atctwo/clock25/extras/images/web_main.png

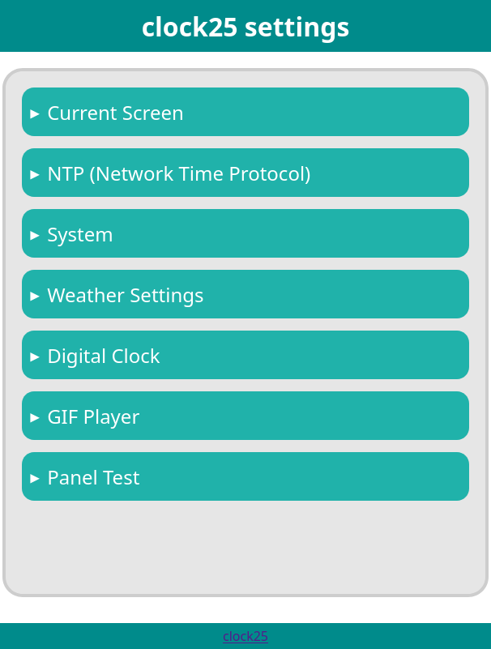
extras/images/web_main.png
