atctwo/clock25/pcb/clock25/clock25.kicad_sch

## KiCad design pcb/clock25/clock25.kicad_sch (2023-04-29)

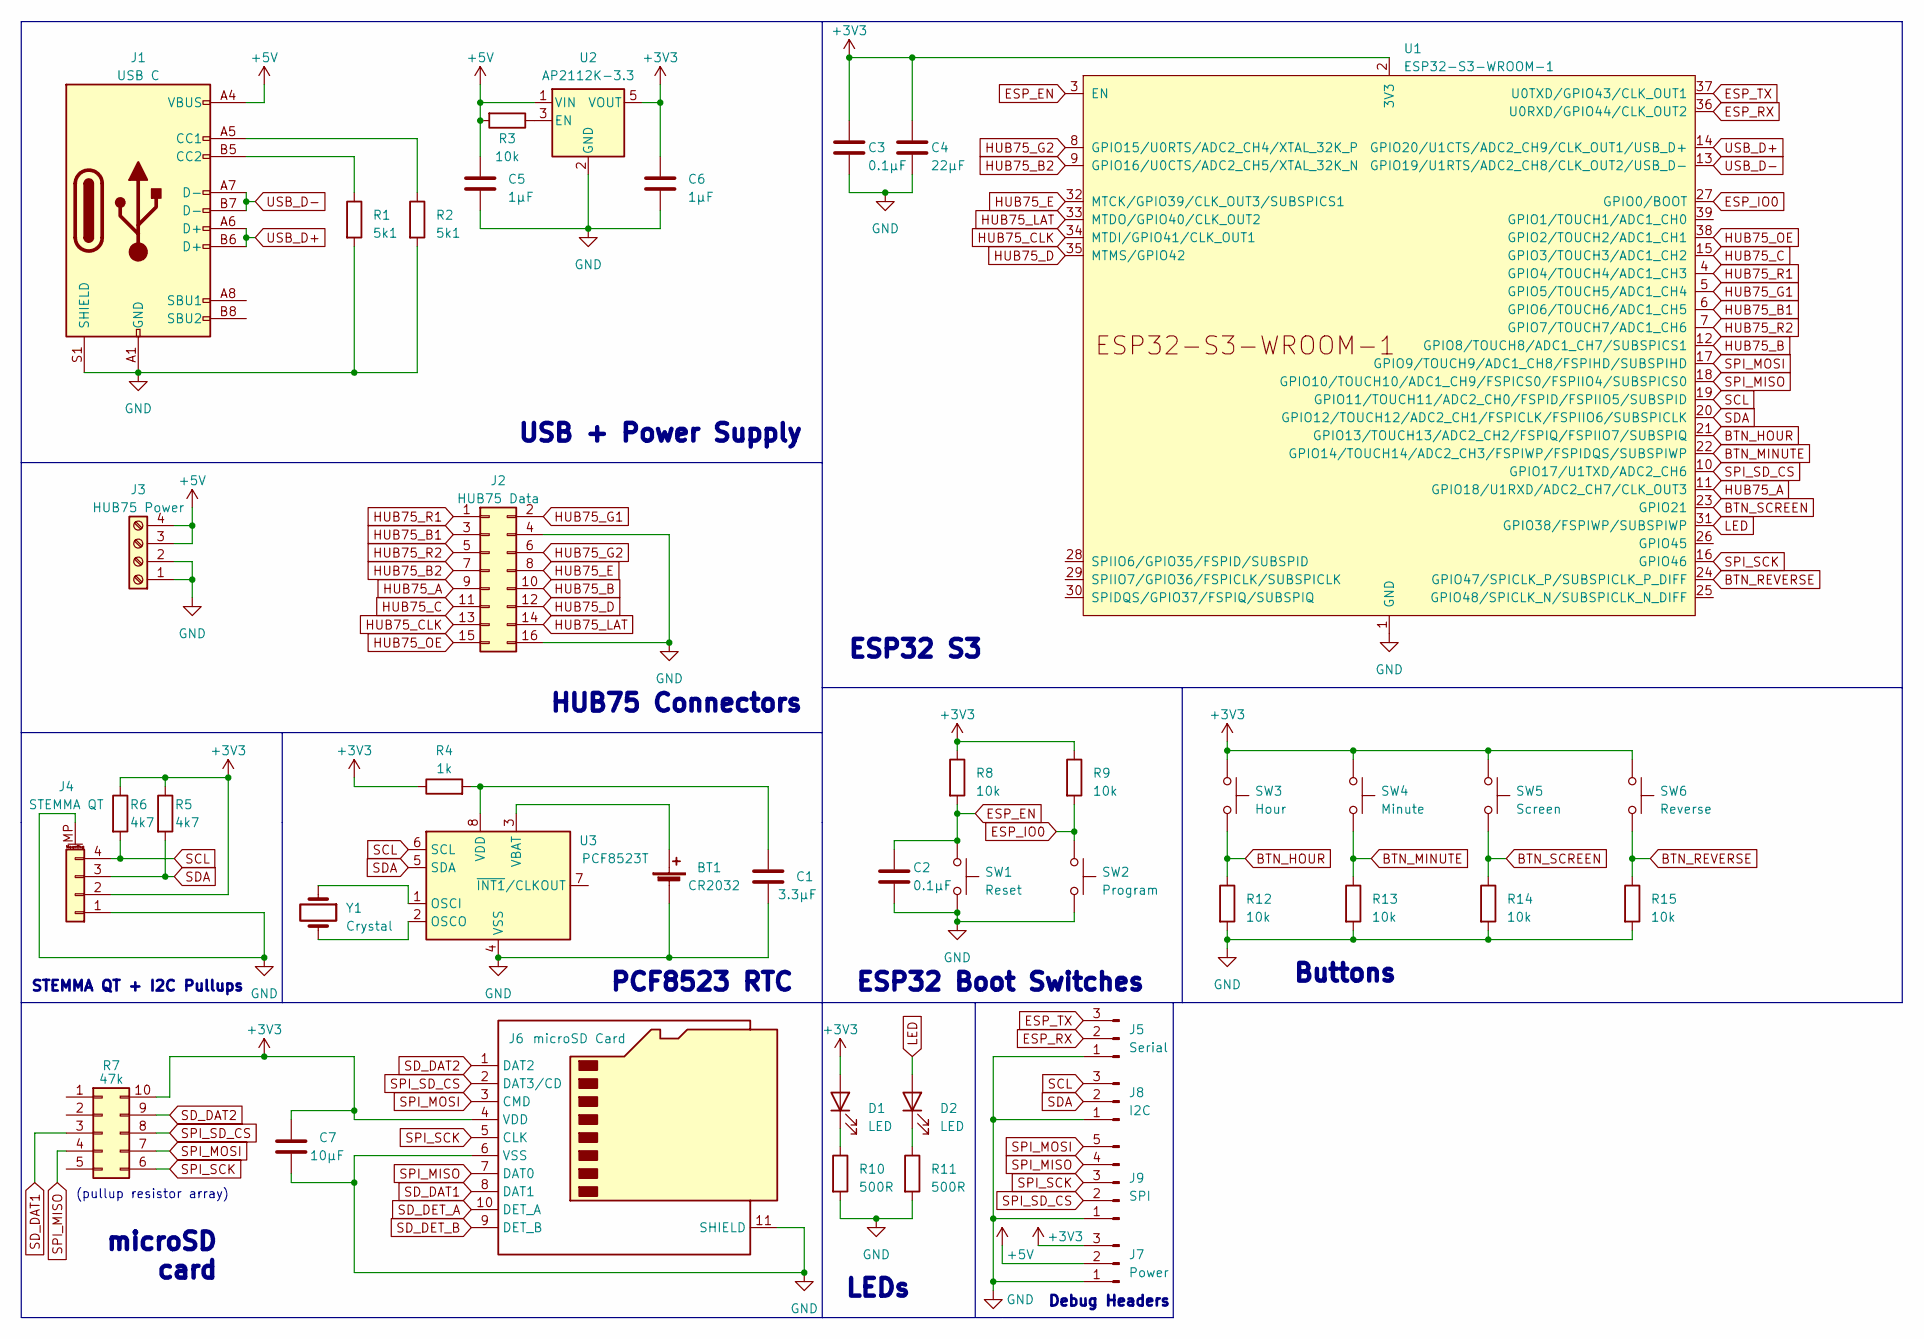
[picture p7: schematic clock25.kicad_sch]

Parts:
BT1: CR2032; BatteryHolder_Keystone_3034_1x20mm
C1: 3.3µF; C_0603_1608Metric
C2, C3: 0.1µF; C_0603_1608Metric
C4: 22µF; C_0603_1608Metric
C5, C6: 1µF; C_0603_1608Metric
C7: 10µF; C_0603_1608Metric
D1, D2: LED; LED_0805_2012Metric
J1: USB C; USB_C_Receptacle_JAE_DX07S016JA1R1500
J2: HUB75 Data; IDC-Header_2x08_P2.54mm_Vertical
J3: HUB75 Power; TerminalBlock_Phoenix_PT-1,5-4-5.0-H_1x04_P5.00mm_Horizontal
J4: STEMMA QT; JST_SH_SM04B-SRSS-TB_1x04-1MP_P1.00mm_Horizontal
J5: Serial; PinSocket_1x03_P2.54mm_Vertical
J6: microSD Card; microSD_HC_Hirose_DM3AT-SF-PEJM5
J7: Power; PinSocket_1x03_P2.54mm_Vertical
J8: I2C; PinSocket_1x03_P2.54mm_Vertical
J9: SPI; PinSocket_1x05_P2.54mm_Vertical
R1, R2: 5k1; R_0603_1608Metric
R3, R8, R9, R12, R13, R14, R15: 10k; R_0603_1608Metric
R4: 1k; R_0603_1608Metric
R5, R6: 4k7; R_0603_1608Metric
R7: 47k; R_Array_Convex_5x1206
R10, R11: 500R; R_0603_1608Metric
SW1: Reset; SW_PUSH_6mm
SW2: Program; SW_PUSH_6mm
SW3: Hour; SW_PUSH_6mm
SW4: Minute; SW_PUSH_6mm
SW5: Screen; SW_PUSH_6mm
SW6: Reverse; SW_PUSH_6mm
U1: ESP32-S3-WROOM-1
U2: AP2112K-3.3; SOT-23-5
U3: PCF8523T; SOIC-8_3.9x4.9mm_P1.27mm
Y1: Crystal; Crystal_C38-LF_D3.0mm_L8.0mm_Horizontal

Connections:
+3V3: C3.1, C4.1, C6.1, C7.1, D1.2 (A), J4.2, J6.4 (VDD), J7.3, R4.1, R5.1, R6.1, R7.10, R8.1, R9.1, SW3.1, SW4.1, SW5.1, SW6.1, U1.2 (3V3), U2.5 (VOUT)
+5V: C5.1, J1.A4 (VBUS), J1.A9 (VBUS), J1.B4 (VBUS), J1.B9 (VBUS), J3.3, J3.4, J7.2, R3.2, U2.1 (VIN)
BTN_HOUR: R12.1, SW3.2, U1.21 (GPIO13/TOUCH13/ADC2_CH2/FSPIQ/FSPIIO7/S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)
BTN_MINUTE: R13.1, SW4.2, U1.22 (GPIO14/TOUCH14/ADC2_CH3/FSPIWP/FSPIDQS/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)
BTN_REVERSE: R15.1, SW6.2, U1.24 (GPIO47/SPICLK_P/SUBSPICLK_P_DIFF)
BTN_SCREEN: R14.1, SW5.2, U1.23 (GPIO21)
ESP_EN: C2.1, R8.2, SW1.1, U1.3 (EN)
ESP_IO0: R9.2, SW2.1, U1.27 (GPIO0/BOOT)
ESP_RX: J5.2, U1.36 (U0RXD/GPIO44/CLK_OUT2)
ESP_TX: J5.3, U1.37 (U0TXD/GPIO43/CLK_OUT1)
GND: BT1.2 (-), C1.2, C2.2, C3.2, C4.2, C5.2, C6.2, C7.2, J1.A1 (GND), J1.A12 (GND), J1.B1 (GND), J1.B12 (GND), J1.S1 (SHIELD), J2.4, J2.16, J3.1, J3.2, J4.1, J4.MP (MountPin), J5.1, J6.6 (VSS), J6.11 (SHIELD), J7.1, J8.1, J9.1, R1.2, R2.2, R10.2, R11.2, R12.2, R13.2, R14.2, R15.2, SW1.2, SW2.2, U1.1 (GND), U1.40 (GND), U1.41 (GND), U2.2 (GND), U3.4 (VSS)
HUB75_A: J2.9, U1.11 (GPIO18/U1RXD/ADC2_CH7/CLK_OUT3)
HUB75_B: J2.10, U1.12 (GPIO8/TOUCH8/ADC1_CH7/SUBSPICS1)
HUB75_B1: J2.3, U1.6 (GPIO6/TOUCH6/ADC1_CH5)
HUB75_B2: J2.7, U1.9 (GPIO16/U0CTS/ADC2_CH5/XTAL_32K_N)
HUB75_C: J2.11, U1.15 (GPIO3/TOUCH3/ADC1_CH2)
HUB75_CLK: J2.13, U1.34 (MTDI/GPIO41/CLK_OUT1)
HUB75_D: J2.12, U1.35 (MTMS/GPIO42)
HUB75_E: J2.8, U1.32 (MTCK/GPIO39/CLK_OUT3/SUBSPICS1)
HUB75_G1: J2.2, U1.5 (GPIO5/TOUCH5/ADC1_CH4)
HUB75_G2: J2.6, U1.8 (GPIO15/U0RTS/ADC2_CH4/XTAL_32K_P)
HUB75_LAT: J2.14, U1.33 (MTDO/GPIO40/CLK_OUT2)
HUB75_OE: J2.15, U1.38 (GPIO2/TOUCH2/ADC1_CH1)
HUB75_R1: J2.1, U1.4 (GPIO4/TOUCH4/ADC1_CH3)
HUB75_R2: J2.5, U1.7 (GPIO7/TOUCH7/ADC1_CH6)
LED: D2.2 (A), U1.31 (GPIO38/FSPIWP/SUBSPIWP)
unnamed: BT1.1 (+), U3.3 (VBAT)
unnamed: C1.1, R4.2, U3.8 (VDD)
unnamed: D1.1 (K), R10.1
unnamed: D2.1 (K), R11.1
unnamed: J1.A5 (CC1), R2.1
unnamed: J1.B5 (CC2), R1.1
unnamed: R3.1, U2.3 (EN)
unnamed: U3.1 (OSCI), Y1.1
unnamed: U3.2 (OSCO), Y1.2
SCL: J4.4, J8.3, R6.2, U1.19 (GPIO11/TOUCH11/ADC2_CH0/FSPID/FSPIIO5/S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), U3.6 (SCL)
SDA: J4.3, J8.2, R5.2, U1.20 (GPIO12/TOUCH12/ADC2_CH1/FSPICLK/FSPIIO6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), U3.5 (SDA)
SD_DAT1: J6.8 (DAT1), R7.3
SD_DAT2: J6.1 (DAT2), R7.9
SD_DET_A: J6.10 (DET_A)
SD_DET_B: J6.9 (DET_B)
SPI_MISO: J6.7 (DAT0), J9.4, R7.4, U1.18 (GPIO10/TOUCH10/ADC1_CH9/FSPICS0/FSPIIO4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)
SPI_MOSI: J6.3 (CMD), J9.5, R7.7, U1.17 (GPIO9/TOUCH9/ADC1_CH8/FSPIHD/SUBSPIHD)
SPI_SCK: J6.5 (CLK), J9.3, R7.6, U1.16 (GPIO46)
SPI_SD_CS: J6.2 (DAT3/CD), J9.2, R7.8, U1.10 (GPIO17/U1TXD/ADC2_CH6)
USB_D+: J1.A6 (D+), J1.B6 (D+), U1.14 (GPIO20/U1CTS/ADC2_CH9/CLK_OUT1/USB_D+)
USB_D-: J1.A7 (D-), J1.B7 (D-), U1.13 (GPIO19/U1RTS/ADC2_CH8/CLK_OUT2/USB_D-)

Notes on the sheet:
USB + Power Supply
PCF8523 RTC
HUB75 Connectors
ESP32 S3
STEMMA QT + I2C Pullups
ESP32 Boot Switches
LEDs
microSD card
(pullup resistor array)
Debug Headers
Buttons
