atctwo/clock25/src/utility.cpp

#include <utility.h>
#include <math.h>

// from https://stackoverflow.com/a/4654718
bool is_number(const std::string& s)
{
    std::string::const_iterator it = s.begin();
    while (it != s.end() && std::isdigit(*it)) ++it;
    return !s.empty() && it == s.end();
}

// convert a colour in HSV space to RGB
// from https://www.cs.rit.edu/~ncs/color/t_convert.html#RGB%20to%20HSV%20&%20HSV%20to%20RGB
void HSVtoRGB( float *r, float *g, float *b, float h, float s, float v )
{
    int i;
    float f, p, q, t;
    if( s == 0 ) {
        // achromatic (grey)
        *r = *g = *b = v;
        return;
    }
    h /= 60;			// sector 0 to 5
    i = floor( h );
    f = h - i;			// factorial part of h
    p = v * ( 1 - s );
    q = v * ( 1 - s * f );
    t = v * ( 1 - s * ( 1 - f ) );
    switch( i ) {
        case 0:
            *r = v;
            *g = t;
            *b = p;
            break;
        case 1:
            *r = q;
            *g = v;
            *b = p;
            break;
        case 2:
            *r = p;
            *g = v;
            *b = t;
            break;
        case 3:
            *r = p;
            *g = q;
            *b = v;
            break;
        case 4:
            *r = t;
            *g = p;
            *b = v;
            break;
        default:		// case 5:
            *r = v;
            *g = p;
            *b = q;
            break;
    }
}

// RGB888 to RGB565
// adapted from https://afterthoughtsoftware.com/posts/convert-rgb888-to-rgb565
uint16_t rgb888torgb565(uint8_t red, uint8_t green, uint8_t blue)
{
    uint16_t b = (blue >> 3) & 0x1f;
    uint16_t g = ((green >> 2) & 0x3f) << 5;
    uint16_t r = ((red >> 3) & 0x1f) << 11;

    return (uint16_t) (r | g | b);
}

//from http://www.andrewnoske.com/wiki/Code_-_heatmaps_and_color_gradients
void getHeatMapColor(float value, float *red, float *green, float *blue, std::vector<std::array<float, 3>> heatmap)
{
    // A static array of 4 colors:  (blue,   green,  yellow,  red) using {r,g,b} for each.

    int idx1;        // |-- Our desired color will be between these two indexes in "color".
    int idx2;        // |
    float fractBetween = 0;  // Fraction between "idx1" and "idx2" where our value is.

    if(value <= 0)      {  idx1 = idx2 = 0;            }    // accounts for an input <=0
    else if(value >= 1)  {  idx1 = idx2 = heatmap.size() - 1; }    // accounts for an input >=0
    else
    {
        value = value * (heatmap.size() - 1);        // Will multiply value by 3.
        idx1  = floor(value);                  // Our desired color will be after this index.
        idx2  = idx1+1;                        // ... and before this index (inclusive).
        fractBetween = value - float(idx1);    // Distance between the two indexes (0-1).
    }

    *red   = (heatmap[idx2][0] - heatmap[idx1][0])*fractBetween + heatmap[idx1][0];
    *green = (heatmap[idx2][1] - heatmap[idx1][1])*fractBetween + heatmap[idx1][1];
    *blue  = (heatmap[idx2][2] - heatmap[idx1][2])*fractBetween + heatmap[idx1][2];
}
